whollender/SuperAudioBoard/SAB_To_RPi/SAB_To_RPi.sch

## KiCad design SAB_To_RPi/SAB_To_RPi.sch (2015-08-20)

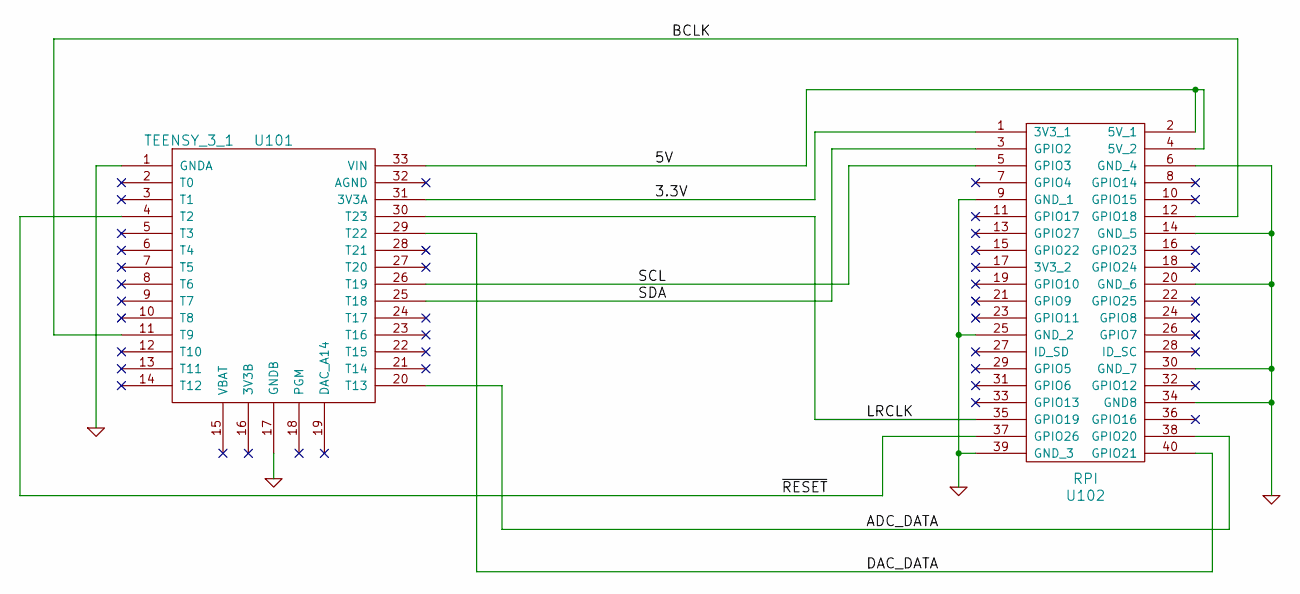
[picture p26: schematic SAB_To_RPi.sch]

Parts:
U101: TEENSY_3_1
U102: RPI

Connections:
3.3V: U101.31 (3V3A), U102.1 (3V3_1)
5V: U101.33 (VIN), U102.2 (5V_1), U102.4 (5V_2)
ADC_DATA: U101.20 (T13), U102.38 (GPIO20)
BCLK: U101.11 (T9), U102.12 (GPIO18)
DAC_DATA: U101.29 (T22), U102.40 (GPIO21)
GND: U101.1 (GNDA), U101.17 (GNDB), U102.6 (GND_4), U102.9 (GND_1), U102.14 (GND_5), U102.20 (GND_6), U102.25 (GND_2), U102.30 (GND_7), U102.34 (GND8), U102.39 (GND_3)
LRCLK: U101.30 (T23), U102.35 (GPIO19)
SCL: U101.26 (T19), U102.5 (GPIO3)
SDA: U101.25 (T18), U102.3 (GPIO2)
~RESET: U101.4 (T2), U102.37 (GPIO26)
