whollender/SuperAudioBoard/KiCADFiles/Board/AnalogInputBuffer.sch

## KiCad design KiCADFiles/Board/AnalogInputBuffer.sch (2015-05-10)

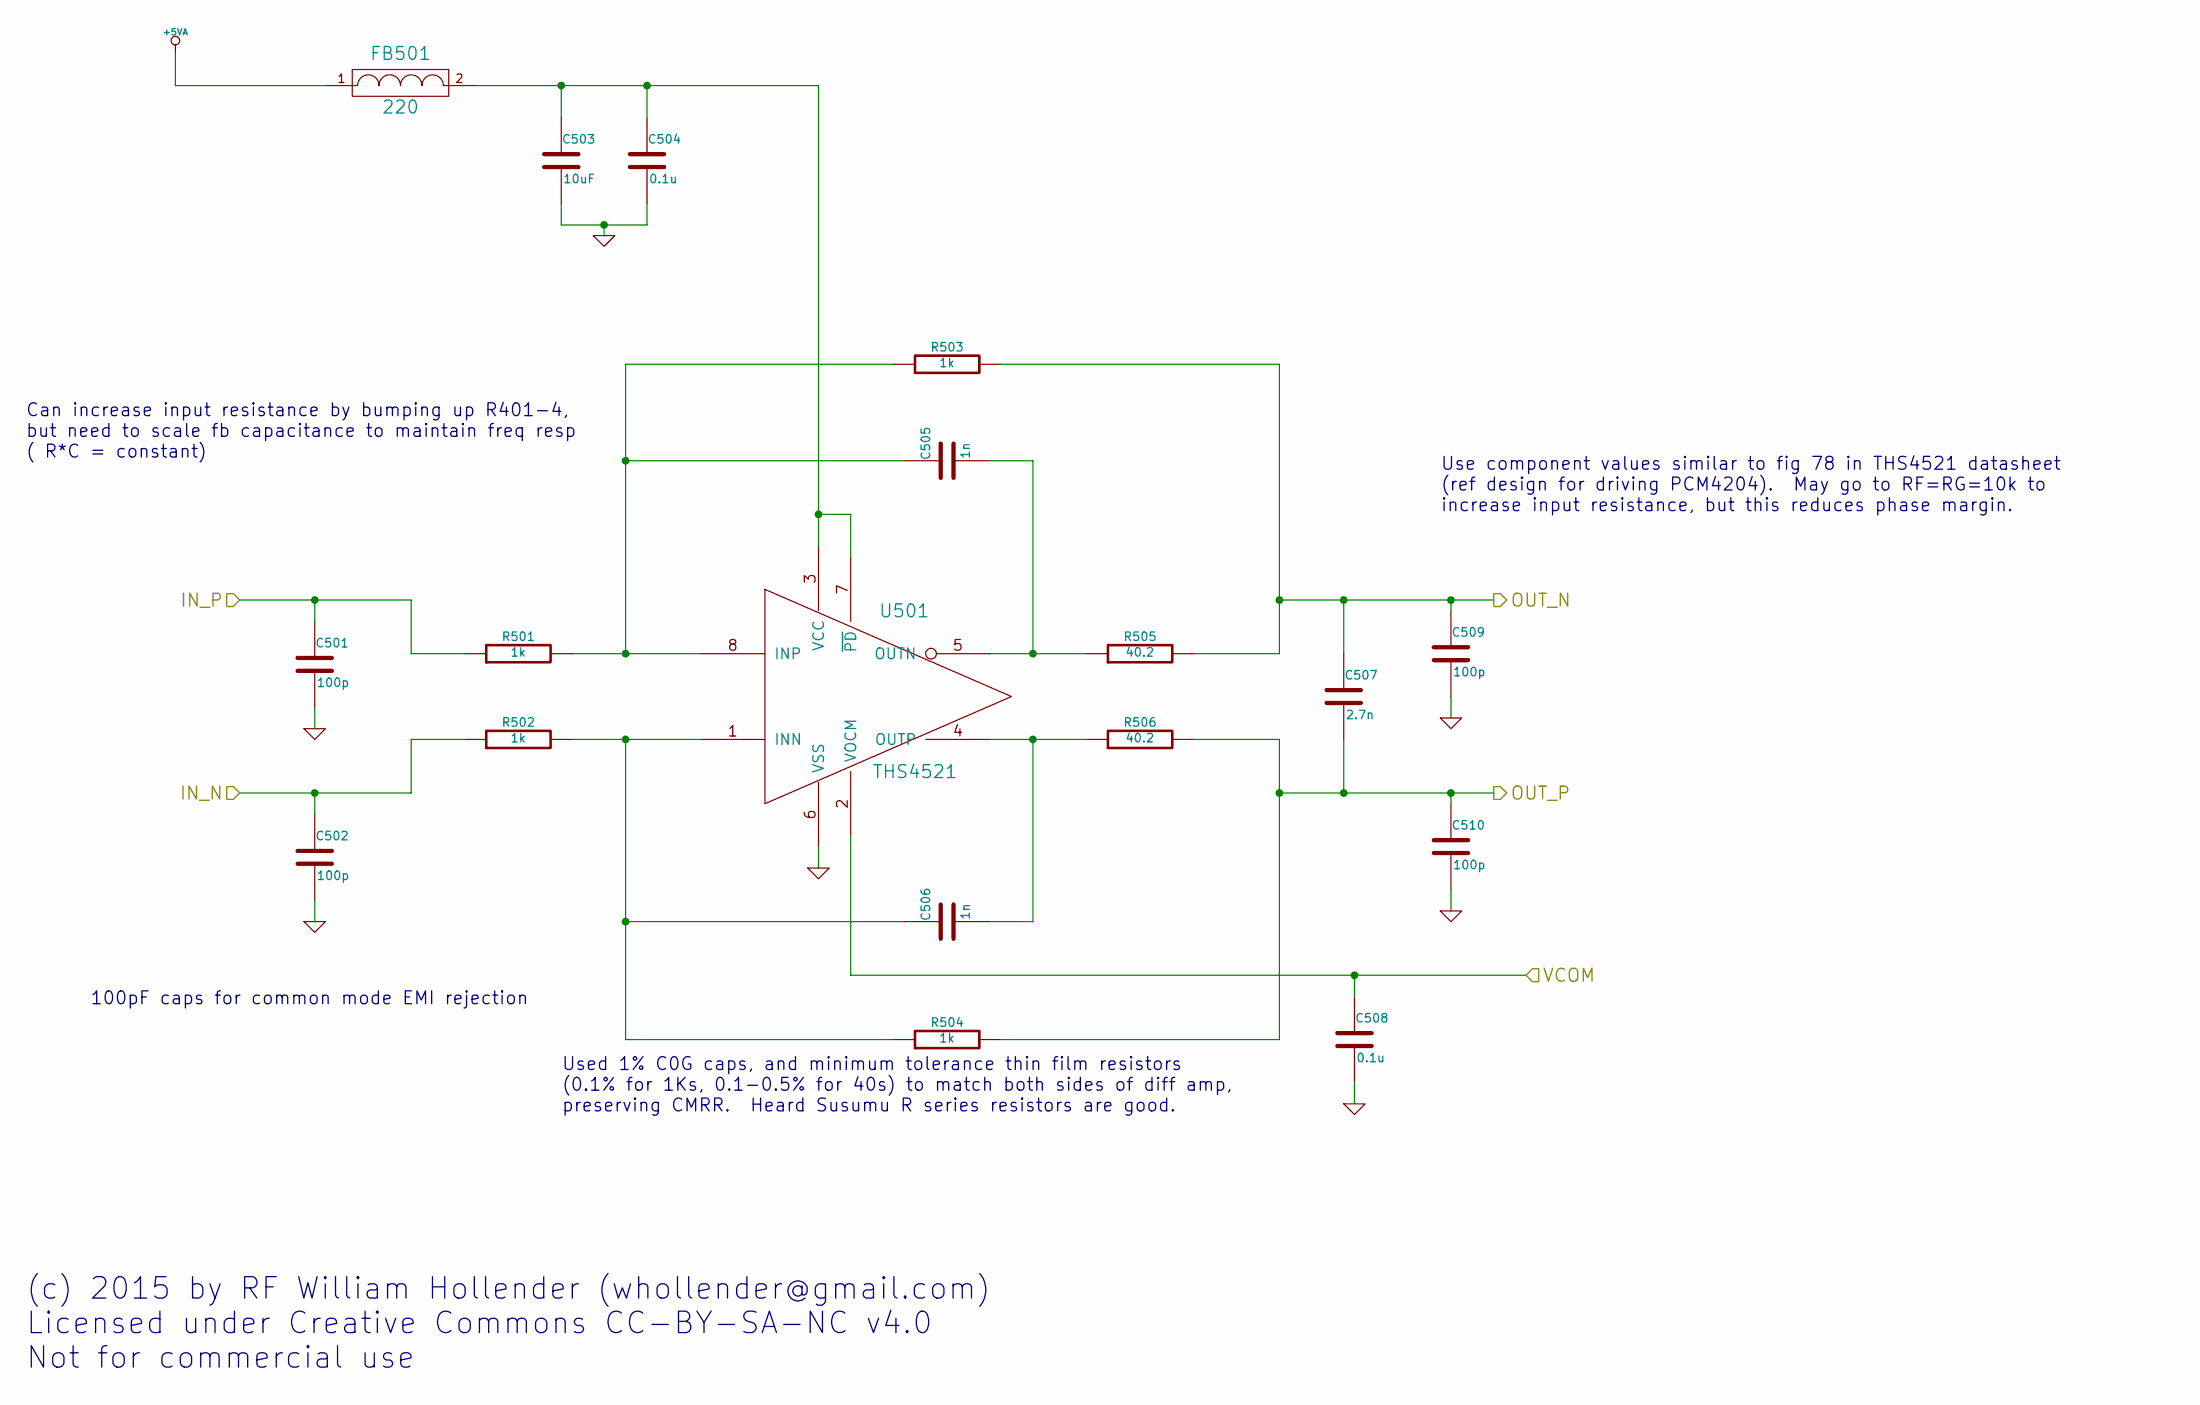
[picture p27: schematic AnalogInputBuffer.sch]

Parts:
C401, C402, C409, C410: 100p; MFG1 PN GRM1885C1H101JA01D
C403: 10uF; MFG1 PN GRM32DR71E106KA12
C404, C408: 0.1u; MFG1 PN GRM188R71E104KA01
C405, C406: 1n; MFG1 PN GRM2165C1H102FA01D
C407: 2.7n; MFG1 PN GRM2165C1H272JA01D
FB401: 220; MFG1 PN BLM18AG221SN1
R401, R402, R403, R404: 1k; MFG1 PN RG2012P-102-B-T5
R405, R406: 40.2; MFG1 PN RR1220Q-40R2-D-M
U401: THS4521; MFG1 PN THS4521ID

Connections:
+5VA: FB401.1
GND: C401.2, C402.2, C403.2, C404.2, C408.2, C409.2, C410.2, U401.6 (VSS)
IN_N: C402.1, R402.1
IN_P: C401.1, R401.1
unnamed: C403.1, C404.1, FB401.2, U401.3 (VCC), U401.7 (~PD)
unnamed: C405.1, R401.2, R403.1, U401.8 (INP)
unnamed: C405.2, R405.1, U401.5 (OUTN)
unnamed: C406.1, R402.2, R404.1, U401.1 (INN)
unnamed: C406.2, R406.1, U401.4 (OUTP)
OUT_N: C407.1, C409.1, R403.2, R405.2
OUT_P: C407.2, C410.1, R404.2, R406.2
VCOM: C408.1, U401.2 (VOCM)

Notes on the sheet:
Use component values similar to fig 78 in THS4521 datasheet (ref design for driving PCM4204). May go to RF=RG=10k to increase input resistance, but this reduces phase margin.
100pF caps for common mode EMI rejection
Used 1% C0G caps, and minimum tolerance thin film resistors (0.1% for 1Ks, 0.1-0.5% for 40s) to match both sides of diff amp, preserving CMRR. Heard Susumu R series resistors are good.
Can increase input resistance by bumping up R401-4, but need to scale fb capacitance to maintain freq resp ( R*C = constant)
(c) 2015 by RF William Hollender (whollender@gmail.com) Licensed under Creative Commons CC-BY-SA-NC v4.0 Not for commercial use
