whollender/SuperAudioBoard/KiCADFiles/Board/AnalogOutputBuffer.sch

## KiCad design KiCADFiles/Board/AnalogOutputBuffer.sch (2015-05-10)

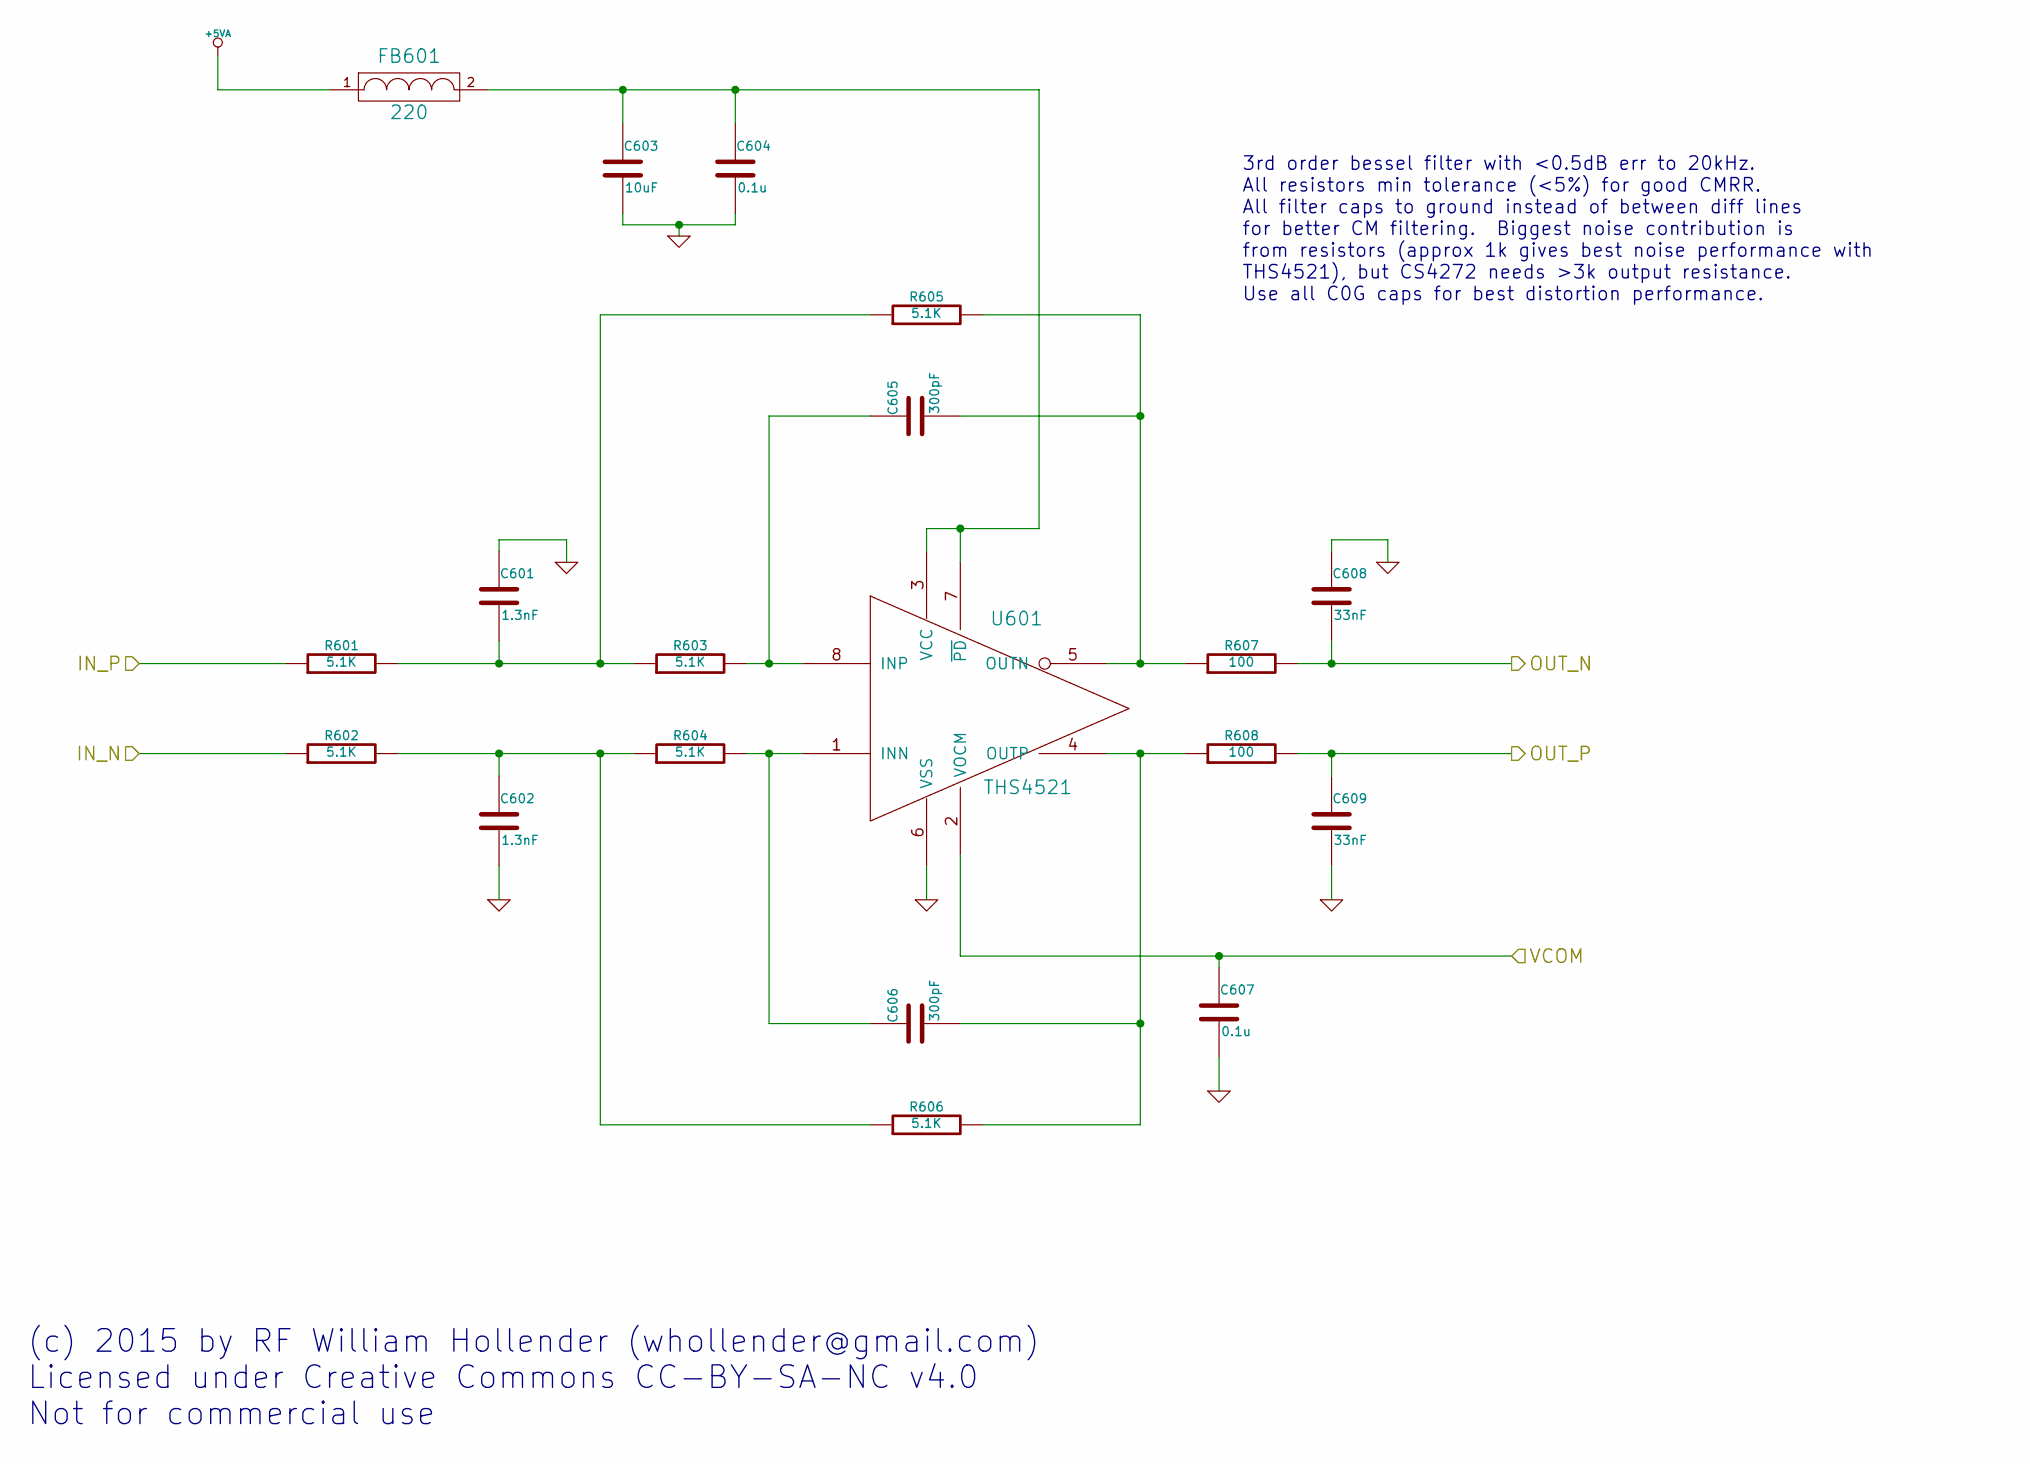
[picture p28: schematic AnalogOutputBuffer.sch]

Parts:
C601, C602: 1.3nF; MFG1 PN GRM1885C1H132JA01D
C603: 10uF; MFG1 PN GRM32DR71E106KA12
C604, C607: 0.1u; MFG1 PN GRM188R71E104KA01
C605, C606: 300pF; MFG1 PN GRM1885C1H301JA01D
C608, C609: 33nF; MFG1 PN C2012C0G1E333J125AA
FB601: 220; MFG1 PN BLM18AG221SN1
R601, R602, R603, R604, R605, R606: 5.1K; MFG1 PN RG2012P-512-B-T5
R607, R608: 100; MFG1 PN RG2012P-101-B-T5
U601: THS4521; MFG1 PN THS4521ID

Connections:
+5VA: FB601.1
GND: C601.1, C602.2, C603.2, C604.2, C607.2, C608.1, C609.2, U601.6 (VSS)
IN_N: R602.1
IN_P: R601.1
unnamed: C601.2, R601.2, R603.1, R605.1
unnamed: C602.1, R602.2, R604.1, R606.1
unnamed: C603.1, C604.1, FB601.2, U601.3 (VCC), U601.7 (~PD)
unnamed: C605.1, R603.2, U601.8 (INP)
unnamed: C605.2, R605.2, R607.1, U601.5 (OUTN)
unnamed: C606.1, R604.2, U601.1 (INN)
unnamed: C606.2, R606.2, R608.1, U601.4 (OUTP)
OUT_N: C608.2, R607.2
OUT_P: C609.1, R608.2
VCOM: C607.1, U601.2 (VOCM)

Notes on the sheet:
3rd order bessel filter with <0.5dB err to 20kHz. All resistors min tolerance (<5%) for good CMRR. All filter caps to ground instead of between diff lines for better CM filtering. Biggest noise contribution is from resistors (approx 1k gives best noise performance with THS4521), but CS4272 needs >3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
(c) 2015 by RF William Hollender (whollender@gmail.com) Licensed under Creative Commons CC-BY-SA-NC v4.0 Not for commercial use
