whollender/SuperAudioBoard/KiCADFiles/Board/CodecAndAnalog.sch

## KiCad design KiCADFiles/Board/CodecAndAnalog.sch (2015-05-10)

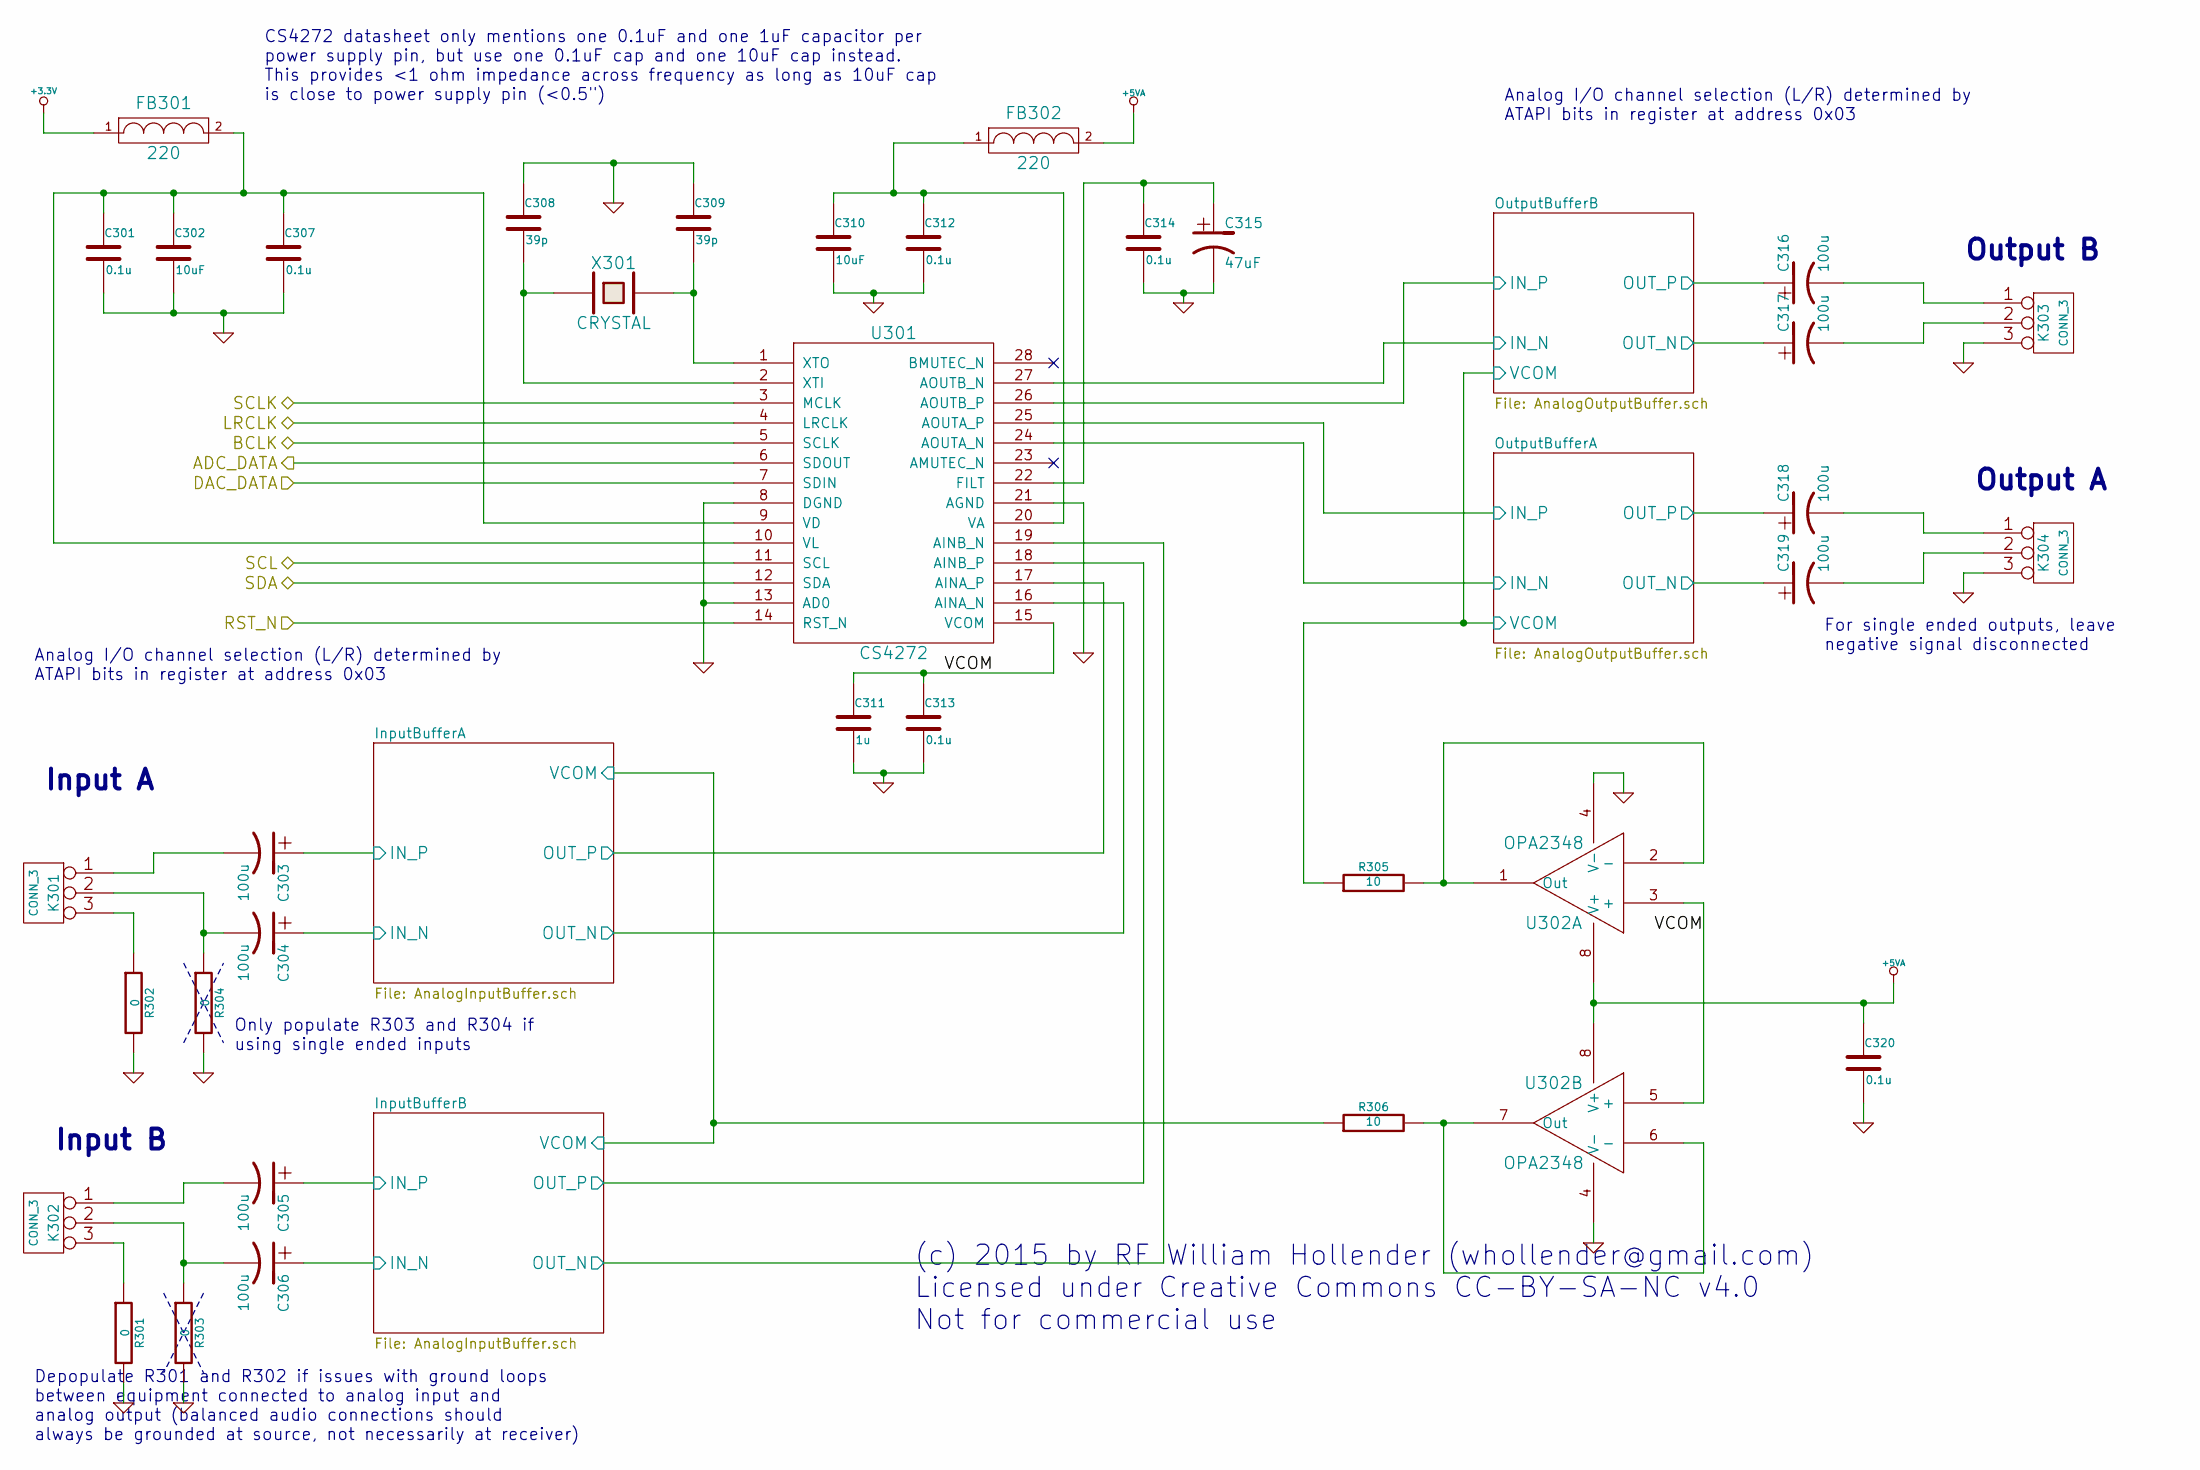
[picture p29: schematic CodecAndAnalog.sch]

Parts:
C301, C307, C312, C313, C314, C320: 0.1u; MFG1 PN GRM188R71E104KA01
C302, C310: 10uF; MFG1 PN GRM32DR71E106KA12
C303, C304, C305, C306, C316, C317, C318, C319: 100u; MFG1 PN UFW1V101MED1TD
C308, C309: 39p; MFG1 PN GRM1885C1H390JA01D
C311: 1u; MFG1 PN C2012X7R1E105K125AB
C315: 47uF; MFG1 PN EDK476M025A9GAA
FB301, FB302: 220; MFG1 PN BLM18AG221SN1
K301, K302, K303, K304: CONN_3
R301, R302, R303, R304: 0; MFG1 PN RC0805JR-070RL
R305, R306: 10; MFG1 PN RC0805JR-0710RL
U301: CS4272; MFG1 PN CS4272-CZZ
U302: OPA2348; MFG1 PN OPA2348AIDR
X301: CRYSTAL; MFG1 PN ECS-245.7-20-5PX-TR

Connections:
+3.3V: FB301.1
+5VA: C320.1, FB302.2, U302.8 (V+)
ADC_DATA: U301.6 (SDOUT)
BCLK: U301.5 (SCLK)
DAC_DATA: U301.7 (SDIN)
GND: C301.2, C302.2, C307.2, C308.1, C309.1, C310.2, C311.2, C312.2, C313.2, C314.2, C315.2, C320.2, K303.3, K304.3, R301.2, R302.2, R303.2, R304.2, U301.8 (DGND), U301.13 (AD0), U301.21 (AGND), U302.4 (V-)
IN_N: C304.1, C306.1, U301.24 (AOUTA_N), U301.27 (AOUTB_N)
IN_P: C303.1, C305.1, U301.25 (AOUTA_P), U301.26 (AOUTB_P)
LRCLK: U301.4 (LRCLK)
unnamed: C301.1, C302.1, C307.1, FB301.2, U301.9 (VD), U301.10 (VL)
unnamed: C303.2, K301.1
unnamed: C304.2, K301.2 (PM), R304.1
unnamed: C305.2, K302.1
unnamed: C306.2, K302.2 (PM), R303.1
unnamed: C308.2, U301.2 (XTI), X301.1
unnamed: C309.2, U301.1 (XTO), X301.2
unnamed: C310.1, C312.1, FB302.1, U301.20 (VA)
unnamed: C314.1, C315.1, U301.22 (FILT)
unnamed: C316.2, K303.1
unnamed: C317.2, K303.2 (PM)
unnamed: C318.2, K304.1
unnamed: C319.2, K304.2 (PM)
unnamed: K301.3, R302.1
unnamed: K302.3, R301.1
unnamed: R305.2, U302.1 (Out), U302.2 (-)
unnamed: R306.2, U302.6 (-), U302.7 (Out)
OUT_N: C317.1, C319.1, U301.16 (AINA_N), U301.19 (AINB_N)
OUT_P: C316.1, C318.1, U301.17 (AINA_P), U301.18 (AINB_P)
RST_N: U301.14 (RST_N)
SCL: U301.11 (SCL)
SCLK: U301.3 (MCLK)
SDA: U301.12 (SDA)
VCOM: C311.1, C313.1, R305.1, R306.1, U301.15 (VCOM), U302.3 (+), U302.5 (+)

Notes on the sheet:
CS4272 datasheet only mentions one 0.1uF and one 1uF capacitor per power supply pin, but use one 0.1uF cap and one 10uF cap instead. This provides <1 ohm impedance across frequency as long as 10uF cap is close to power supply pin (<0.5")
Analog I/O channel selection (L/R) determined by ATAPI bits in register at address 0x03
Input A
Input B
Output A
Output B
Depopulate R301 and R302 if issues with ground loops between equipment connected to analog input and analog output (balanced audio connections should always be grounded at source, not necessarily at receiver)
Only populate R303 and R304 if using single ended inputs
For single ended outputs, leave negative signal disconnected
(c) 2015 by RF William Hollender (whollender@gmail.com) Licensed under Creative Commons CC-BY-SA-NC v4.0 Not for commercial use
