whollender/SuperAudioBoard/KiCADFiles/Board/PowerSupply.sch

## KiCad design KiCADFiles/Board/PowerSupply.sch (2015-05-10)

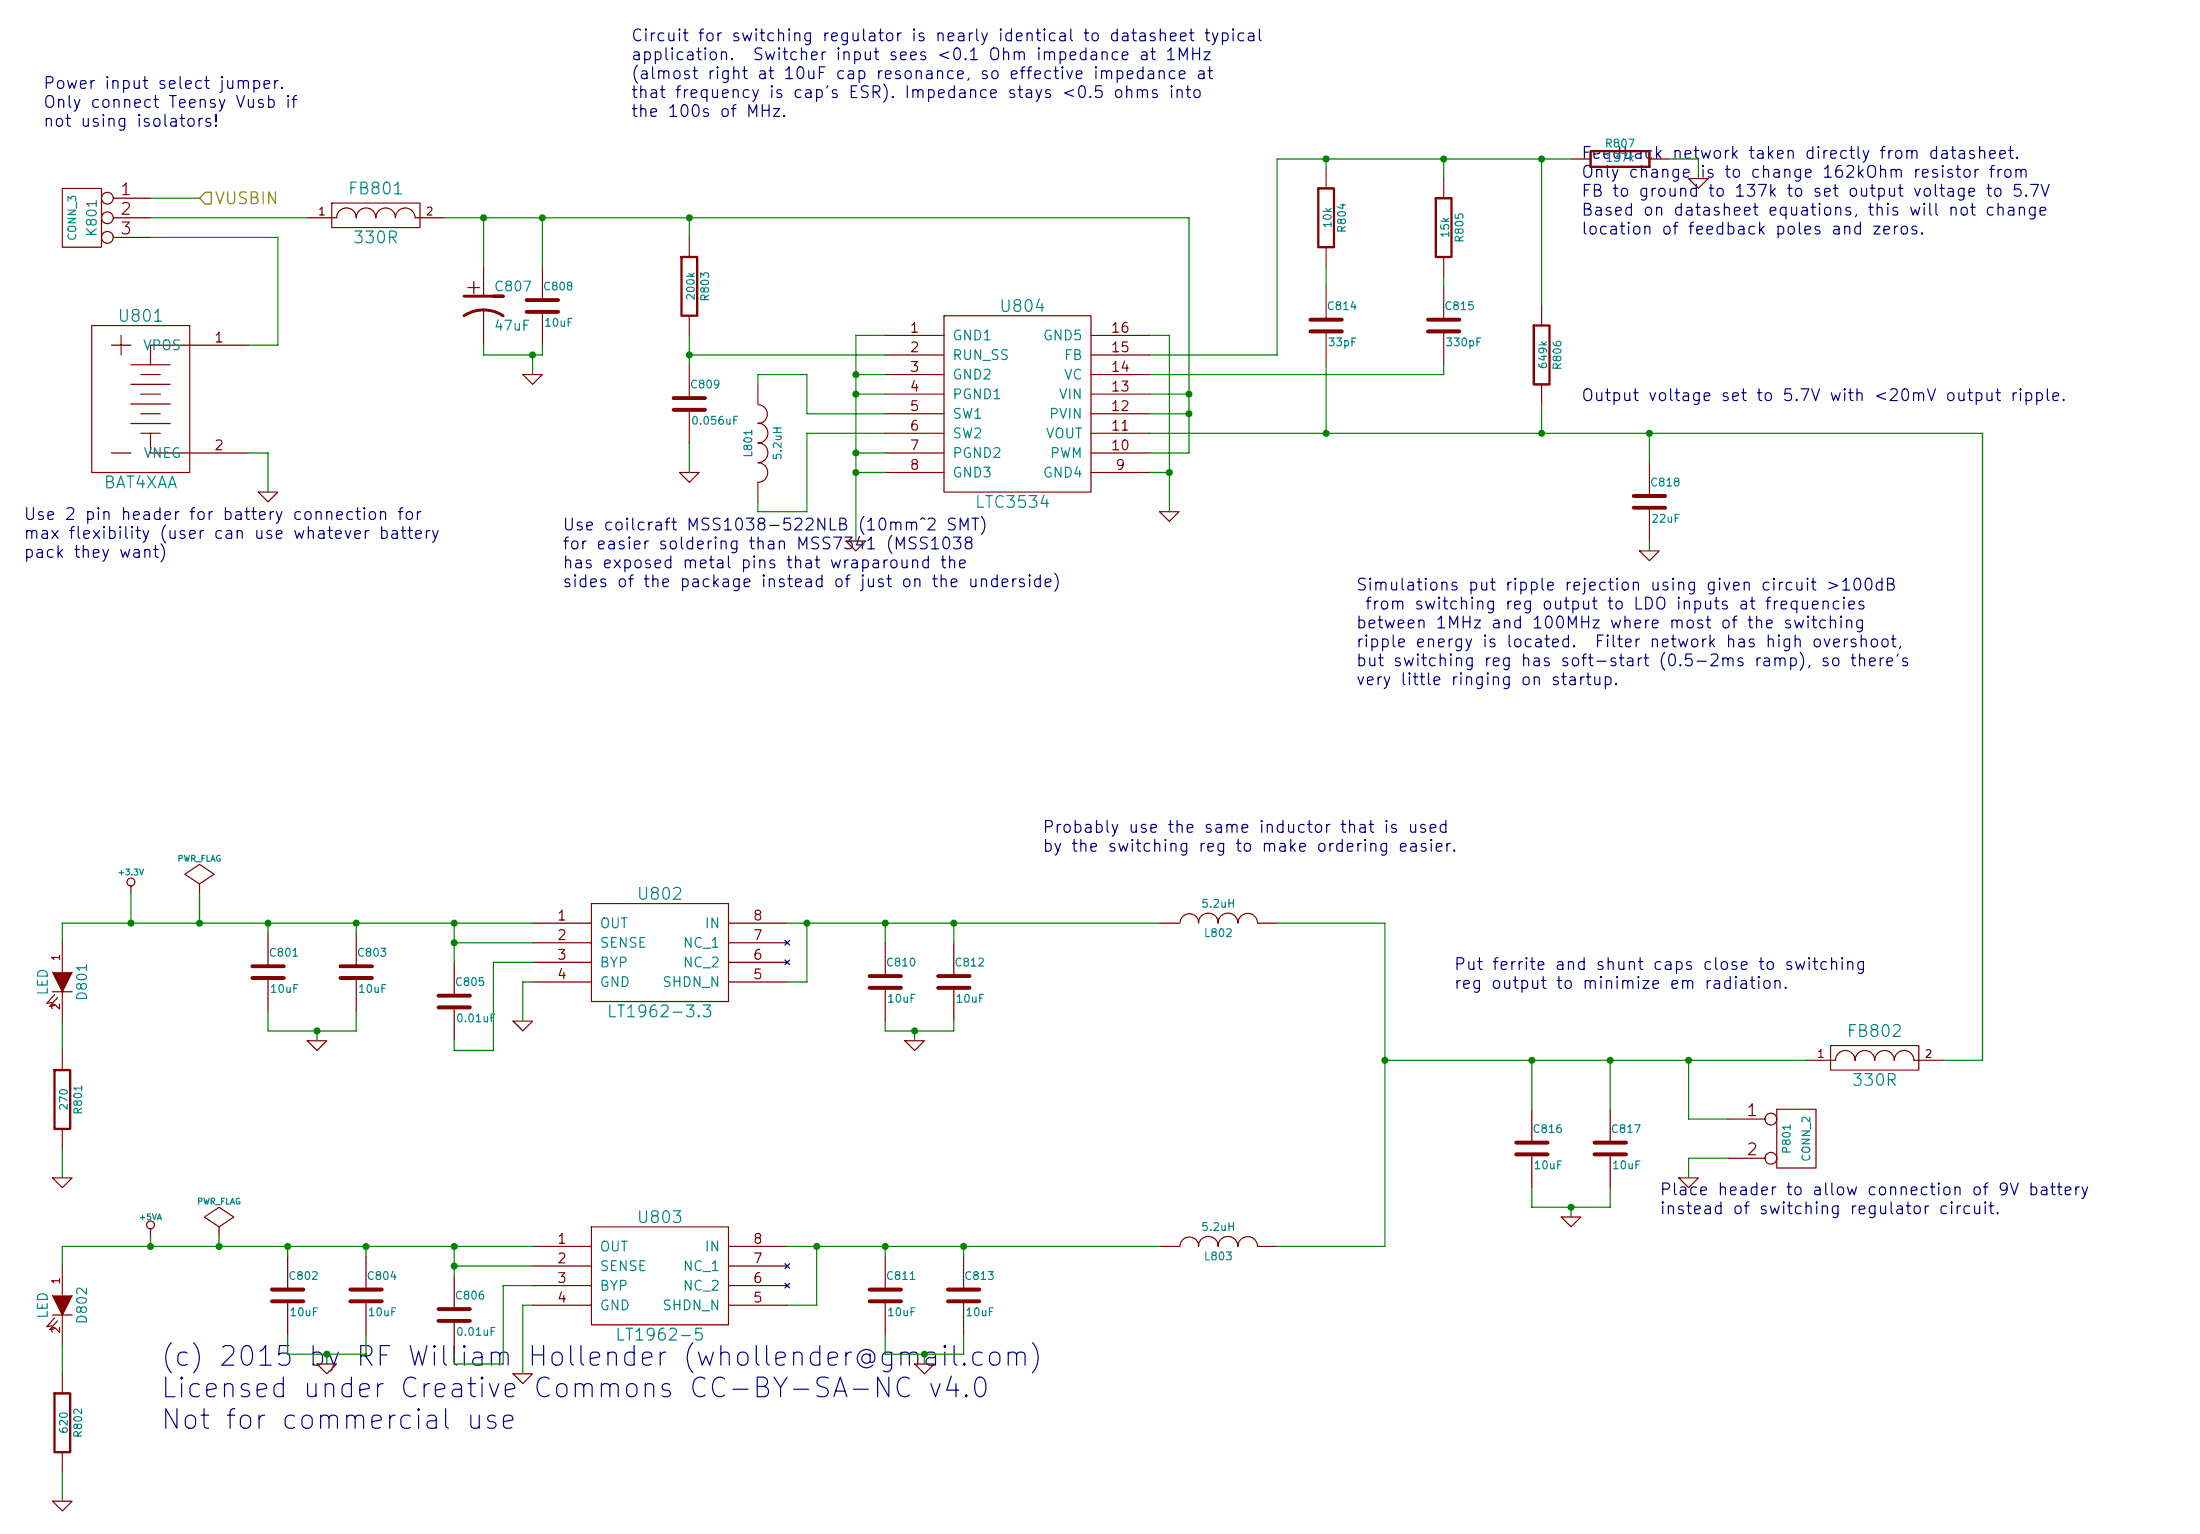
[picture p30: schematic PowerSupply.sch]

Parts:
C801, C802, C803, C804, C808, C810, C811, C812, C813, C816, C817: 10uF; MFG1 PN GRM32DR71E106KA12
C805, C806: 0.01uF; MFG1 PN GRM2195C1H103JA01D
C807: 47uF; MFG1 PN EDK476M025A9GAA
C809: 0.056uF; MFG1 PN 08055C563KAT2A
C814: 33pF; MFG1 PN GRM1885C1H330JA01D
C815: 330pF; MFG1 PN GRM1885C1H331JA01D
C818: 22uF; MFG1 PN GRM32ER71C226KE18L
D801, D802: LED; MFG1 PN APT2012CGCK
FB801, FB802: 330R; MFG1 PN BLM21PG331SN1D
K801: CONN_3
L801, L802, L803: 5.2uH; MFG1 PN MSS1038-522NLB
P801: CONN_2
R801: 270; MFG1 PN ERJ-6GEYJ271V
R802: 620; MFG1 PN ERJ-6GEYJ621V
R803: 200k; MFG1 PN RC0805FR-07200KL
R804: 10k; MFG1 PN RC0603FR-0710KL
R805: 15k; MFG1 PN RC0603FR-0715KL
R806: 649k; MFG1 PN RC0603FR-07649KL
R807: 137k; MFG1 PN RC0603FR-07137KL
U801: BAT4XAA
U802: LT1962-3.3; MFG1 PN LT1962EMS8-3.3#PBF
U803: LT1962-5; MFG1 PN LT1962EMS8-5#PBF-ND
U804: LTC3534; MFG1 PN LTC3534EGN#PBF

Connections:
+3.3V: C801.1, C803.1, C805.1, D801.1 (A), U802.1 (OUT), U802.2 (SENSE)
+5VA: C802.1, C804.1, C806.1, D802.1 (A), U803.1 (OUT), U803.2 (SENSE)
GND: C801.2, C802.2, C803.2, C804.2, C807.2, C808.2, C809.2, C810.2, C811.2, C812.2, C813.2, C816.2, C817.2, C818.2, P801.2 (PM), R801.2, R802.2, R807.1, U801.2 (VNEG), U802.4 (GND), U803.4 (GND), U804.1 (GND1), U804.3 (GND2), U804.4 (PGND1), U804.7 (PGND2), U804.8 (GND3), U804.9 (GND4), U804.16 (GND5)
unnamed: C805.2, U802.3 (BYP)
unnamed: C806.2, U803.3 (BYP)
unnamed: C807.1, C808.1, FB801.2, R803.1, U804.10 (PWM), U804.12 (PVIN), U804.13 (VIN)
unnamed: C809.1, R803.2, U804.2 (RUN_SS)
unnamed: C810.1, C812.1, L802.1, U802.5 (SHDN_N), U802.8 (IN)
unnamed: C811.1, C813.1, L803.1, U803.5 (SHDN_N), U803.8 (IN)
unnamed: C814.1, R804.2
unnamed: C814.2, C818.1, FB802.2, R806.2, U804.11 (VOUT)
unnamed: C815.1, R805.2
unnamed: C815.2, U804.14 (VC)
unnamed: C816.1, C817.1, FB802.1, L802.2, L803.2, P801.1
unnamed: D801.2 (K), R801.1
unnamed: D802.2 (K), R802.1
unnamed: FB801.1, K801.2 (PM)
unnamed: K801.3, U801.1 (VPOS)
unnamed: L801.1, U804.5 (SW1)
unnamed: L801.2, U804.6 (SW2)
unnamed: R804.1, R805.1, R806.1, R807.2, U804.15 (FB)
VUSBIN: K801.1

Notes on the sheet:
Output voltage set to 5.7V with <20mV output ripple.
Put ferrite and shunt caps close to switching reg output to minimize em radiation.
Probably use the same inductor that is used by the switching reg to make ordering easier.
Circuit for switching regulator is nearly identical to datasheet typical application. Switcher input sees <0.1 Ohm impedance at 1MHz (almost right at 10uF cap resonance, so effective impedance at that frequency is cap's ESR). Impedance stays <0.5 ohms into the 100s of MHz.
Use coilcraft MSS1038-522NLB (10mm^2 SMT) for easier soldering than MSS7341 (MSS1038 has exposed metal pins that wraparound the sides of the package instead of just on the underside)
Simulations put ripple rejection using given circuit >100dB from switching reg output to LDO inputs at frequencies between 1MHz and 100MHz where most of the switching ripple energy is located. Filter network has high overshoot, but switching reg has soft-start (0.5-2ms ramp), so there's very little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
Place header to allow connection of 9V battery instead of switching regulator circuit.
Feedback network taken directly from datasheet. Only change is to change 162kOhm resistor from FB to ground to 137k to set output voltage to 5.7V Based on datasheet equations, this will not change location of feedback poles and zeros.
Power input select jumper. Only connect Teensy Vusb if not using isolators!
Use 2 pin header for battery connection for max flexibility (user can use whatever battery pack they want)
(c) 2015 by RF William Hollender (whollender@gmail.com) Licensed under Creative Commons CC-BY-SA-NC v4.0 Not for commercial use
