whollender/SuperAudioBoard/KiCADFiles/Board/TeensyAndDigital.sch

## KiCad design KiCADFiles/Board/TeensyAndDigital.sch (2015-05-10)

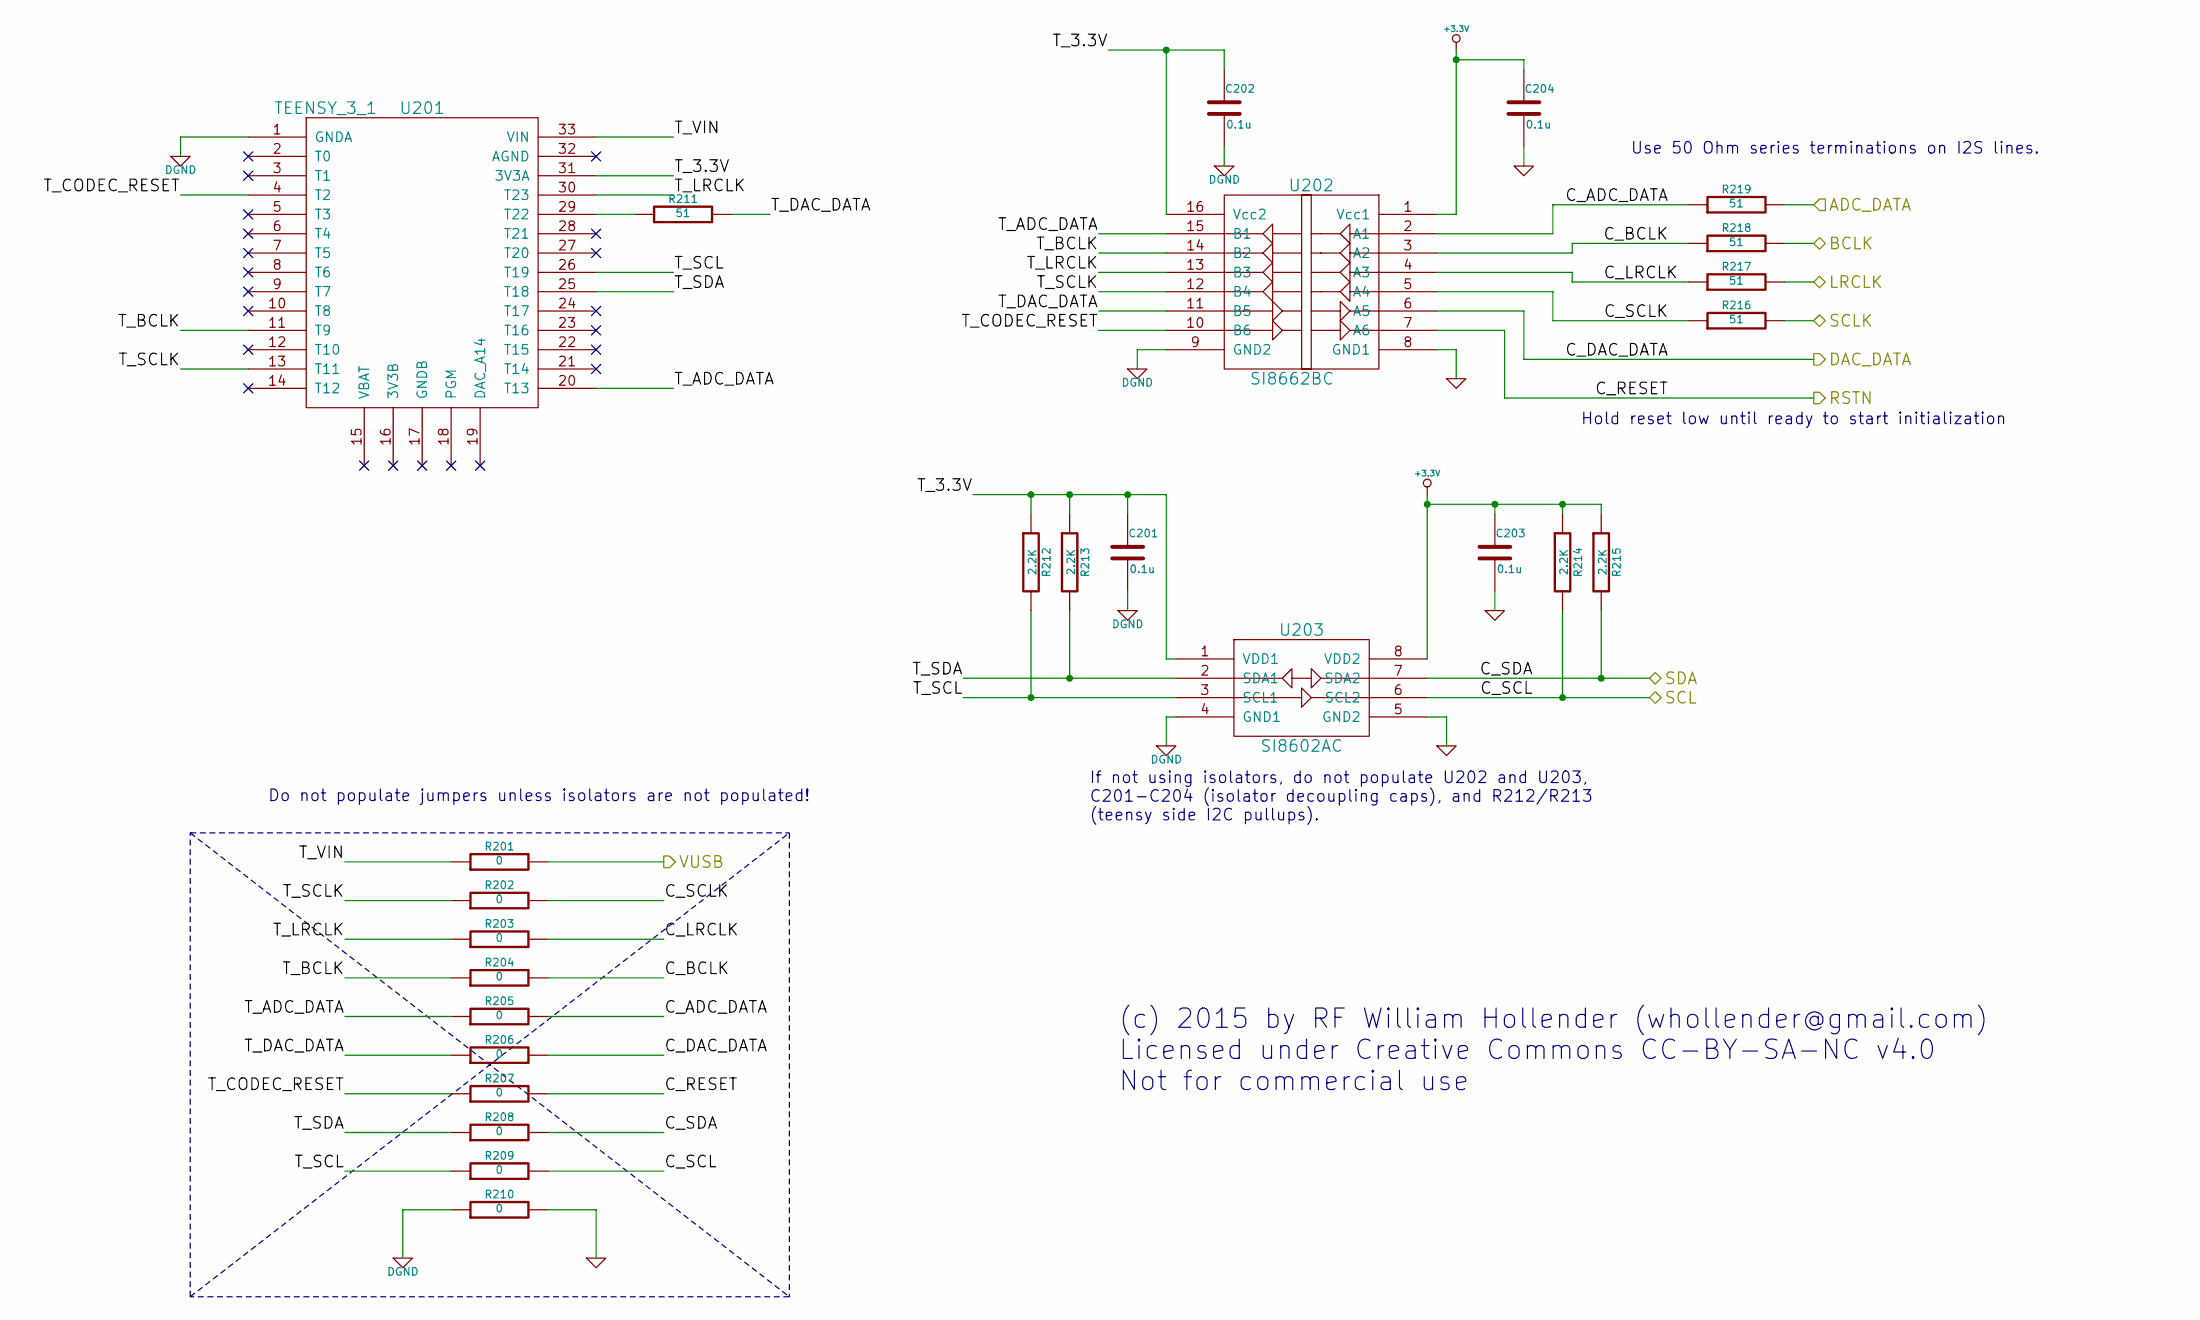
[picture p31: schematic TeensyAndDigital.sch]

Parts:
C201, C202, C203, C204: 0.1u; MFG1 PN GRM188R71E104KA01
R201, R202, R203, R204, R205, R206, R207, R208, R209, R210: 0; MFG1 PN RC0805JR-070RL
R211, R216, R217, R218, R219: 51; MFG1 PN CRCW080551R0JNEA
R212, R213, R214, R215: 2.2K; MFG1 PN RC0805JR-072K2L
U201: TEENSY_3_1; MFG1 PN teensy_3_1
U202: SI8662BC; MFG1 PN SI8662BC
U203: SI8602AC; MFG1 PN SI8602AC

Connections:
+3.3V: C203.1, C204.1, R214.1, R215.1, U202.1 (Vcc1), U203.8 (VDD2)
ADC_DATA: R219.2
BCLK: R218.2
C_ADC_DATA: R205.2, R219.1, U202.2 (A1)
C_BCLK: R204.2, R218.1, U202.3 (A2)
C_DAC_DATA: R206.2, U202.6 (A5)
C_LRCLK: R203.2, R217.1, U202.4 (A3)
C_RESET: R207.2, U202.7 (A6)
C_SCL: R209.2, R214.2, U203.6 (SCL2)
C_SCLK: R202.2, R216.1, U202.5 (A4)
C_SDA: R208.2, R215.2, U203.7 (SDA2)
DGND: C201.2, C202.2, R210.1, U201.1 (GNDA), U202.9 (GND2), U203.4 (GND1)
GND: C203.2, C204.2, R210.2, U202.8 (GND1), U203.5 (GND2)
LRCLK: R217.2
unnamed: R211.1, U201.29 (T22)
SCLK: R216.2
T_3.3V: C201.1, C202.1, R212.1, R213.1, U201.31 (3V3A), U202.16 (Vcc2), U203.1 (VDD1)
T_ADC_DATA: R205.1, U201.20 (T13), U202.15 (B1)
T_BCLK: R204.1, U201.11 (T9), U202.14 (B2)
T_CODEC_RESET: R207.1, U201.4 (T2), U202.10 (B6)
T_DAC_DATA: R206.1, R211.2, U202.11 (B5)
T_LRCLK: R203.1, U201.30 (T23), U202.13 (B3)
T_SCL: R209.1, R212.2, U201.26 (T19), U203.3 (SCL1)
T_SCLK: R202.1, U201.13 (T11), U202.12 (B4)
T_SDA: R208.1, R213.2, U201.25 (T18), U203.2 (SDA1)
T_VIN: R201.1, U201.33 (VIN)
VUSB: R201.2

Notes on the sheet:
Use 50 Ohm series terminations on I2S lines.
Hold reset low until ready to start initialization
Do not populate jumpers unless isolators are not populated!
If not using isolators, do not populate U202 and U203, C201-C204 (isolator decoupling caps), and R212/R213 (teensy side I2C pullups).
(c) 2015 by RF William Hollender (whollender@gmail.com) Licensed under Creative Commons CC-BY-SA-NC v4.0 Not for commercial use
