whollender/SuperAudioBoard/SineTestCode/delay.h

////////////////////////////////////////////////////////////////////////
// delay.h
//
// Delay function prototype
// William Hollender, 5/1/14
////////////////////////////////////////////////////////////////////////

#ifndef DELAY_H
#define DELAY_H

uint32_t micros(void);
void delay(uint32_t ms);

#endif
